romses/Datenzwerg/docs/assets/images/tvoc-sensor.jpg

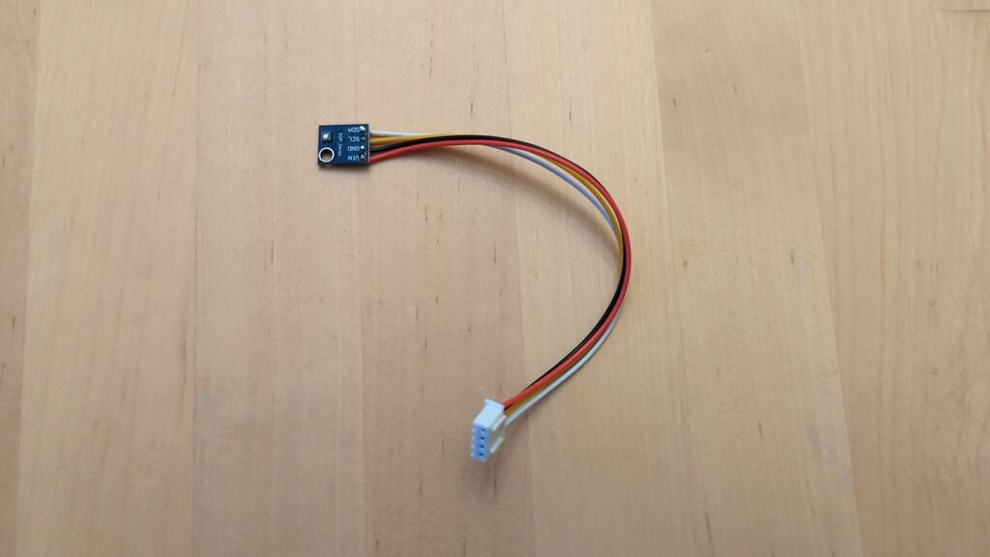
docs/assets/images/tvoc-sensor.jpg
